elisavetchatz/HydrotrackerProject/src/data processing/logging_utils.py

import logging

def setup_logger(logfile='hydrotracker.log'):
    logger = logging.getLogger("HydroLogger")
    logger.setLevel(logging.INFO)

    if not logger.handlers:
        file_handler = logging.FileHandler(logfile)
        formatter = logging.Formatter('[%(asctime)s] %(message)s', datefmt='%Y-%m-%d %H:%M:%S')
        file_handler.setFormatter(formatter)
        logger.addHandler(file_handler)
        
    return logger
